lawesly/Underwater-Glider/Photos/AssemblyEngine.png

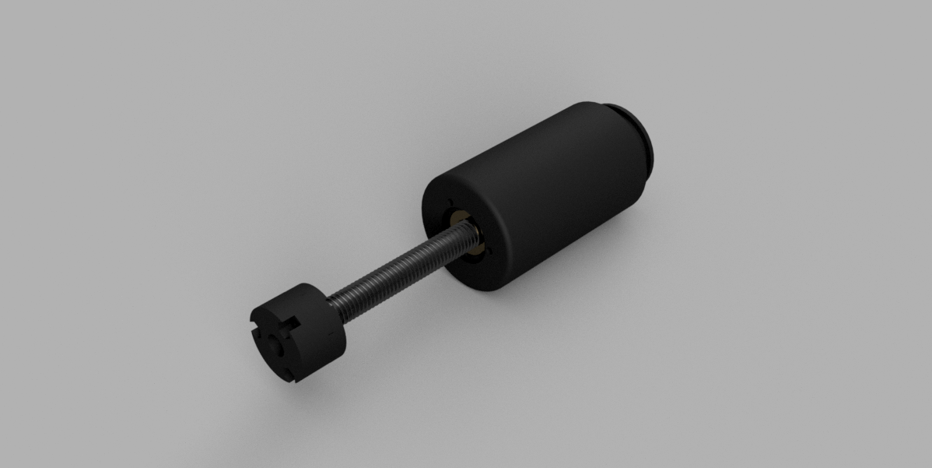
Photos/AssemblyEngine.png
