lawesly/Underwater-Glider/Codes/GliderFunctional/monitorSerial_Angles.ino

void monitorSerial_Angles() {
  Serial.print("angleX : ");
  Serial.println(mpu6050.getAngleX());
  Serial.print("\tangleY : ");
  Serial.print(mpu6050.getAngleY());
  Serial.print("\tangleZ : ");
  Serial.println(mpu6050.getAngleZ());
}
